mfolejewski/FEMTO/Photos/Femto_module_01.png

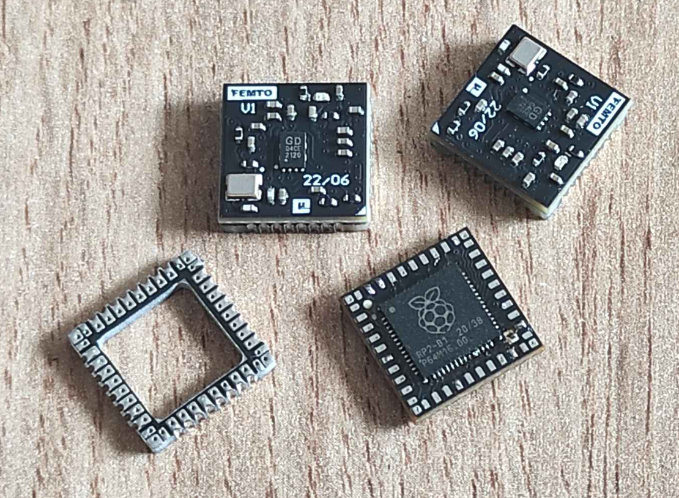
Photos/Femto_module_01.png
