mfolejewski/FEMTO/Photos/Femto_module_02.png

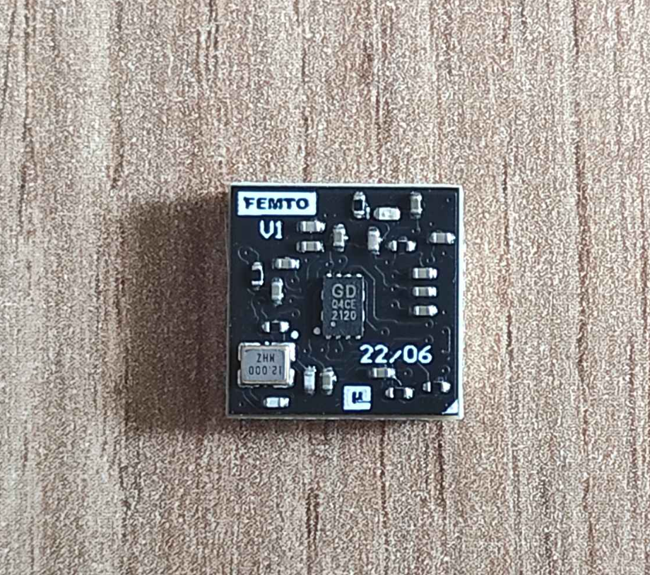
Photos/Femto_module_02.png
