mfolejewski/FEMTO/Photos/Femto_module_03.png

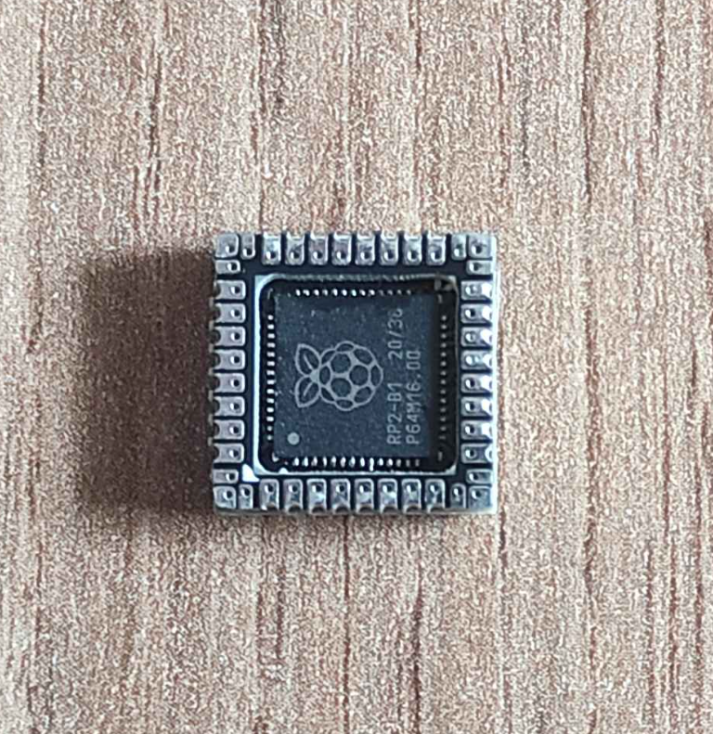
Photos/Femto_module_03.png
