mfolejewski/FEMTO/Photos/Femto_module_07.png

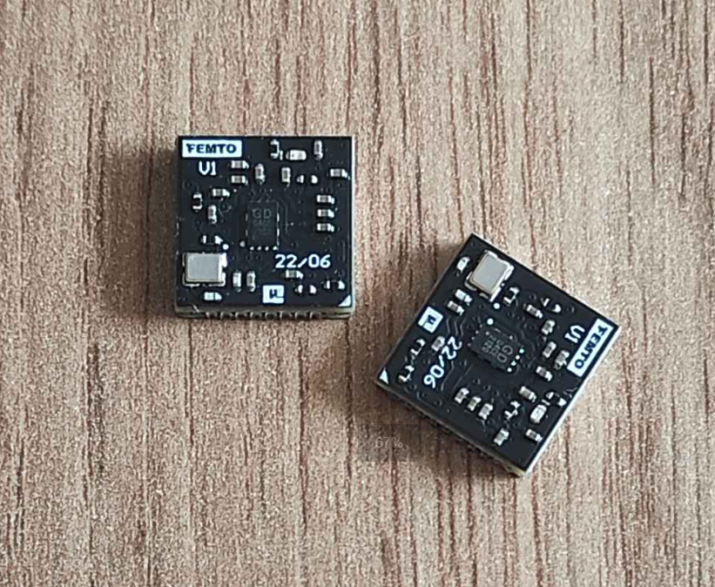
Photos/Femto_module_07.png
