mfolejewski/FEMTO/Photos/Femto_module_08.png

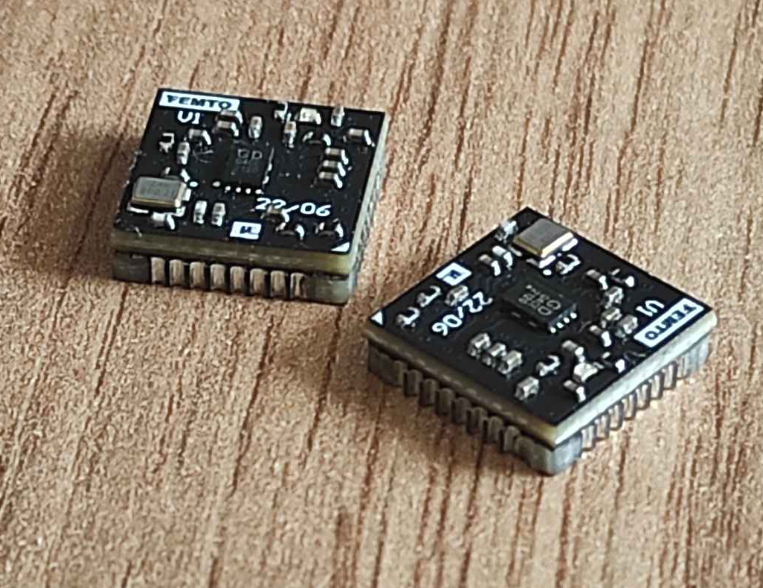
Photos/Femto_module_08.png
