mfolejewski/FEMTO/Photos/Femto_Module_Raspberry_Pico_02.png

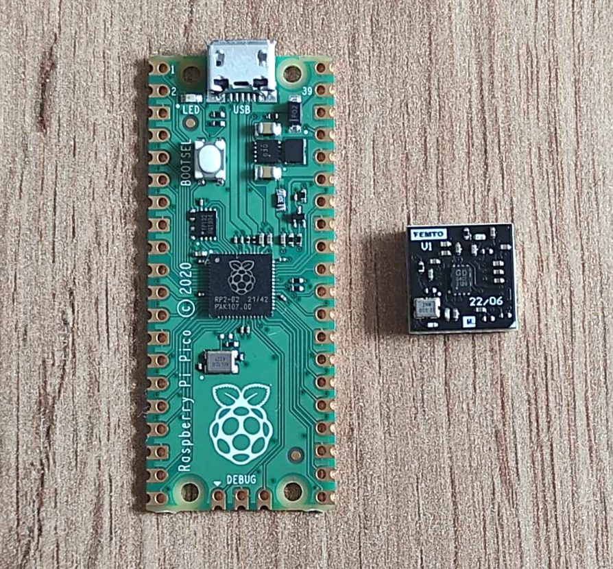
Photos/Femto_Module_Raspberry_Pico_02.png
