mfolejewski/FEMTO/Photos/Femto_Module_Raspberry_Pico_03.png

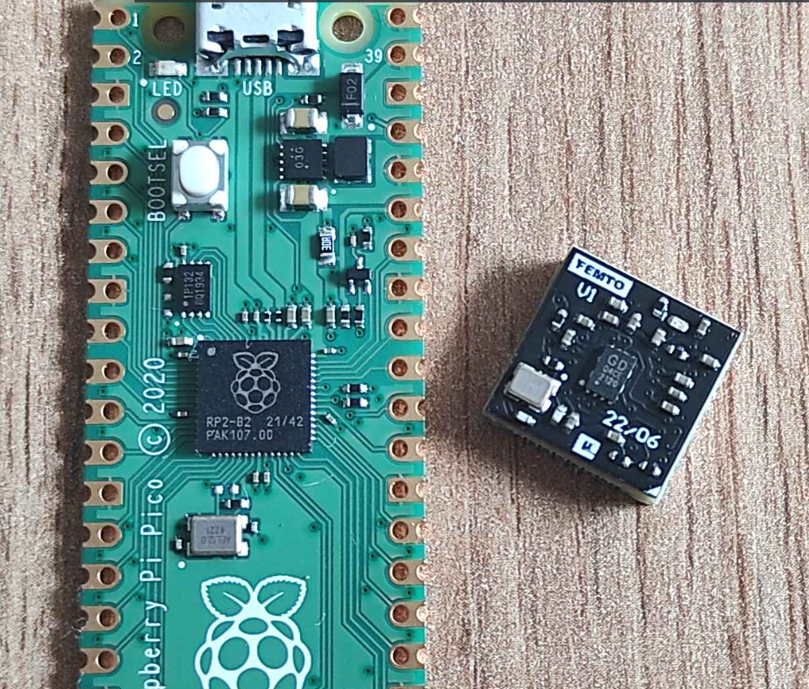
Photos/Femto_Module_Raspberry_Pico_03.png
