mfolejewski/FEMTO/Photos/Femto_Module_Raspberry_Pico_04.png

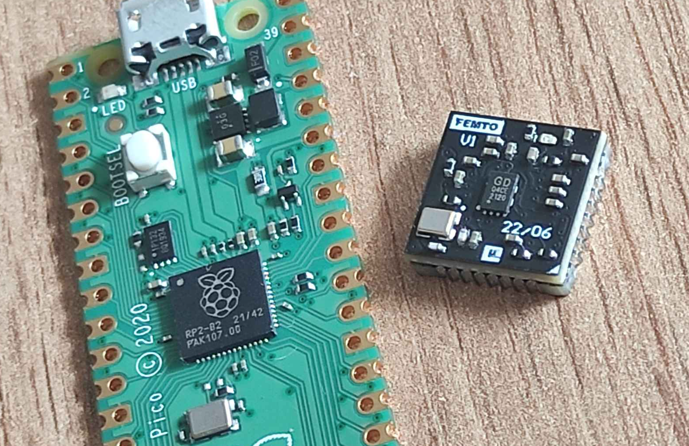
Photos/Femto_Module_Raspberry_Pico_04.png
