mfolejewski/FEMTO/source_files/Kicad/Module/PCB_file_2d_view.png

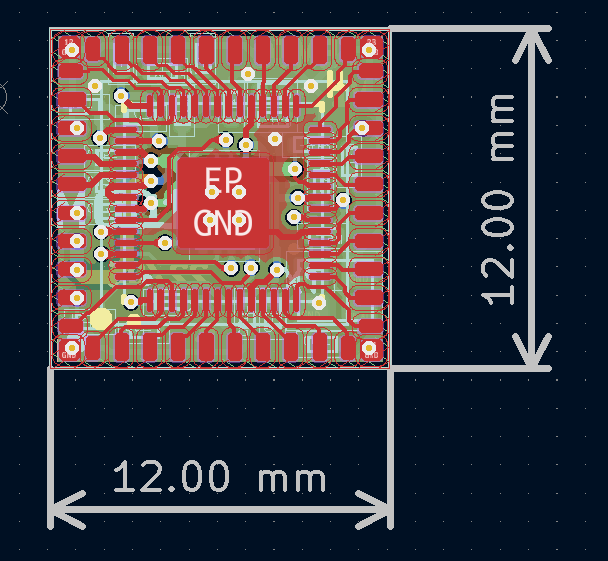
source_files/Kicad/Module/PCB_file_2d_view.png
