mfolejewski/FEMTO/source_files/Kicad/Module/PCB_file_3d_view_bot.png

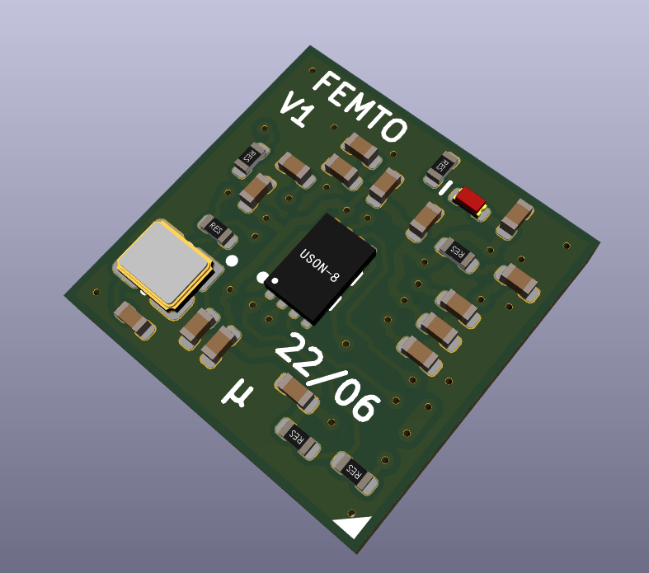
source_files/Kicad/Module/PCB_file_3d_view_bot.png
