mfolejewski/FEMTO/Photos/Femto_tester_03.png

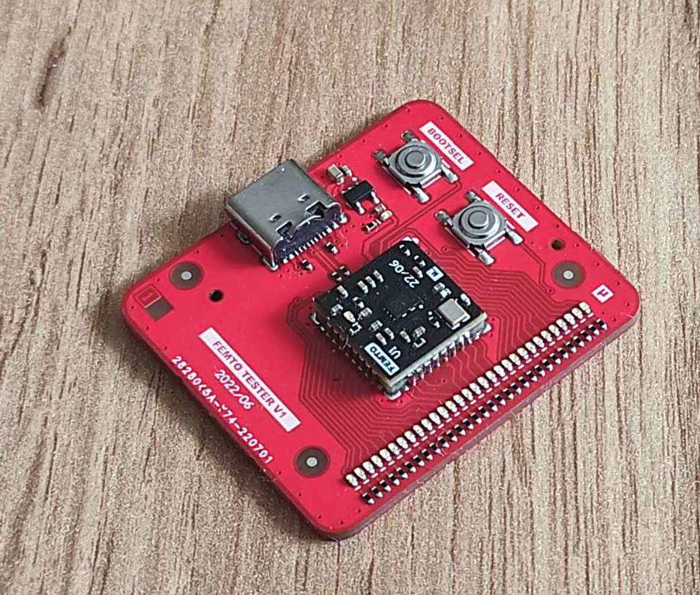
Photos/Femto_tester_03.png
