mfolejewski/FEMTO/Photos/Femto_tester_04.png

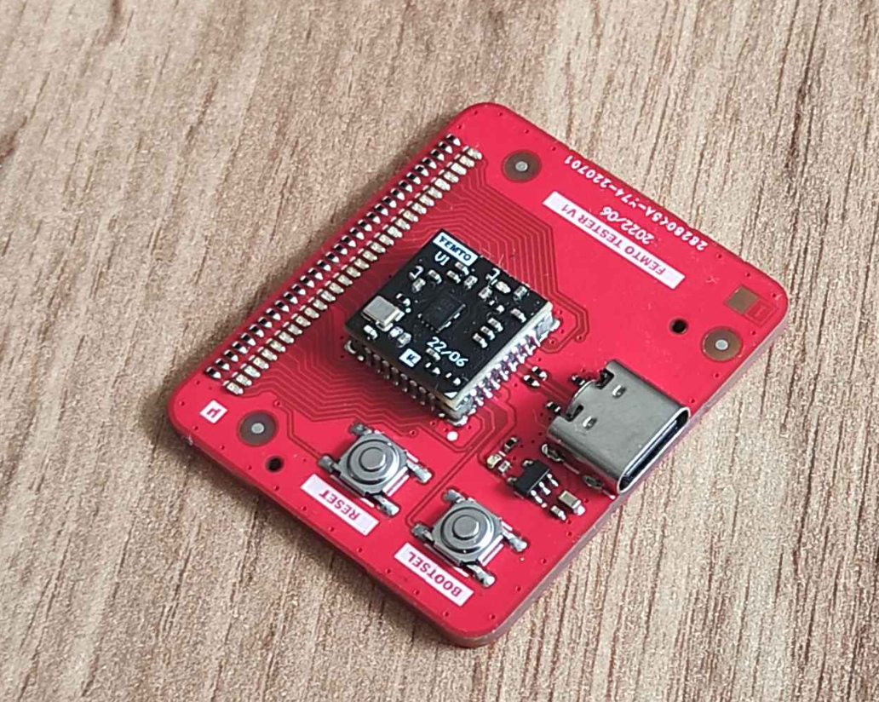
Photos/Femto_tester_04.png
