mfolejewski/FEMTO/source_files/Altium_Designer/Tester/PCB_file_2d_view.png

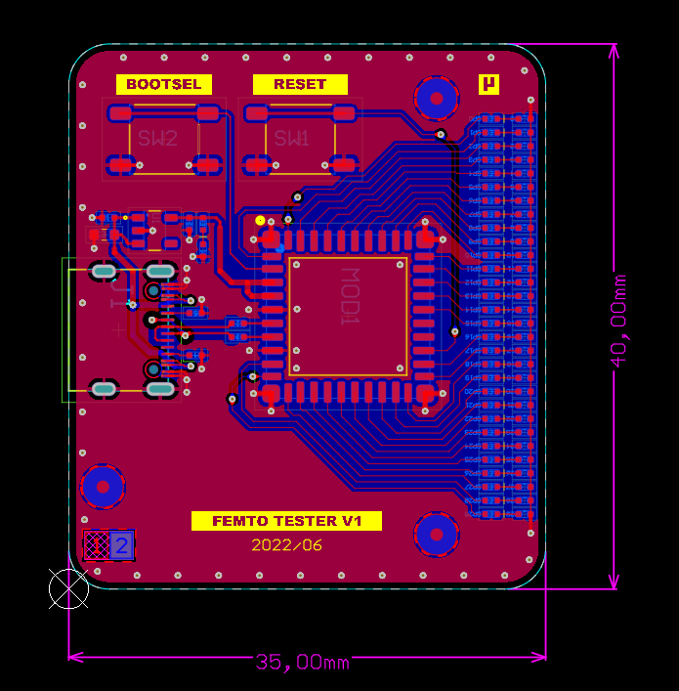
source_files/Altium_Designer/Tester/PCB_file_2d_view.png
