mfolejewski/FEMTO/source_files/Altium_Designer/Tester/PCB_file_3d_view_bot.png

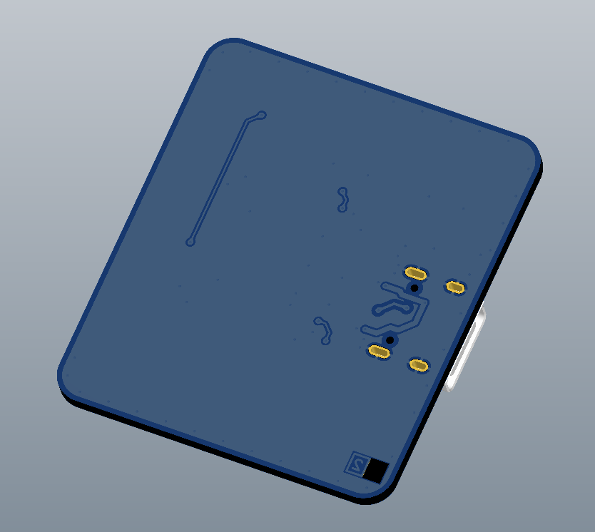
source_files/Altium_Designer/Tester/PCB_file_3d_view_bot.png
