mfolejewski/FEMTO/source_files/Altium_Designer/Tester/PCB_file_3d_view_top.png

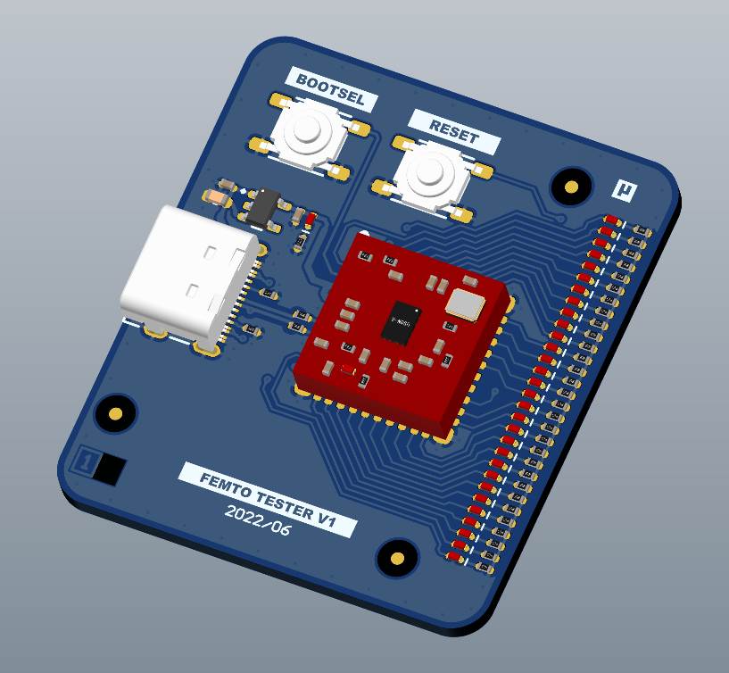
source_files/Altium_Designer/Tester/PCB_file_3d_view_top.png
