mfolejewski/FEMTO/source_files/Kicad/Tester/PCB_file_2d_view.png

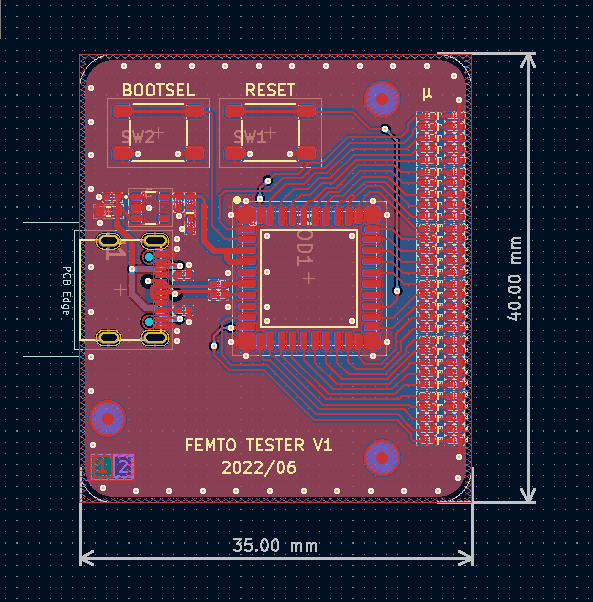
source_files/Kicad/Tester/PCB_file_2d_view.png
