mfolejewski/FEMTO/source_files/Kicad/Tester/PCB_file_3d_view.png

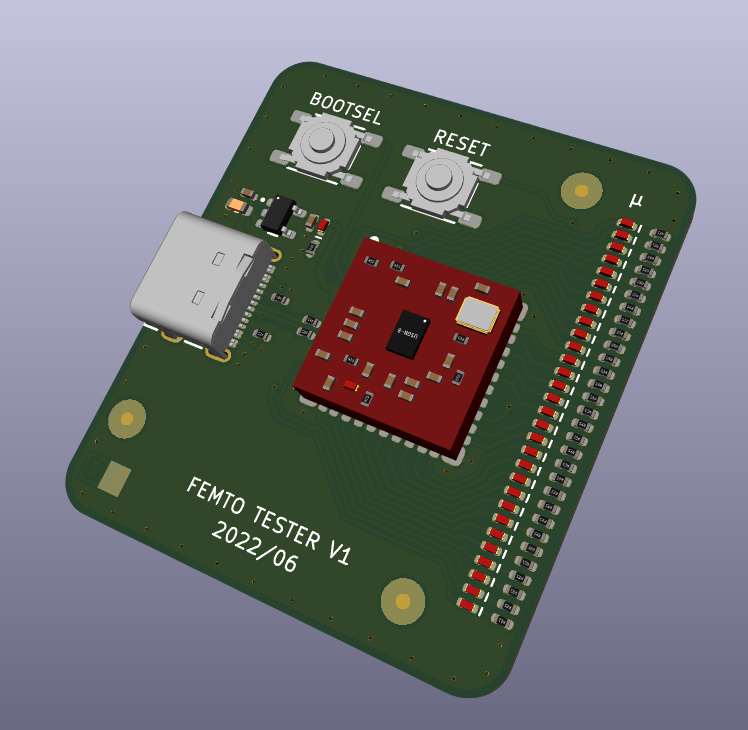
source_files/Kicad/Tester/PCB_file_3d_view.png
